pu2clr/Magnetic_Loop_Antenna_Tuner/images/bluetooth_hc05.jpg

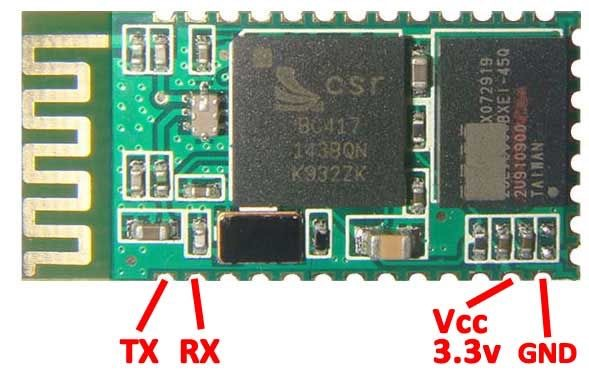
images/bluetooth_hc05.jpg
