pu2clr/Magnetic_Loop_Antenna_Tuner/images/BTAndroid00.png

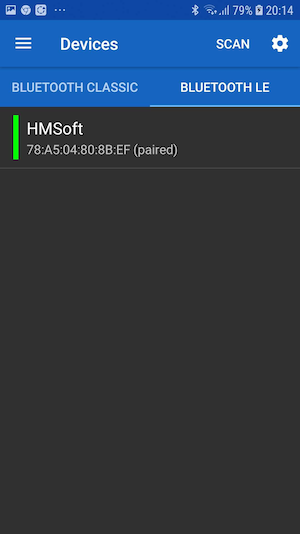
images/BTAndroid00.png
