pu2clr/Magnetic_Loop_Antenna_Tuner/images/photo01.jpg

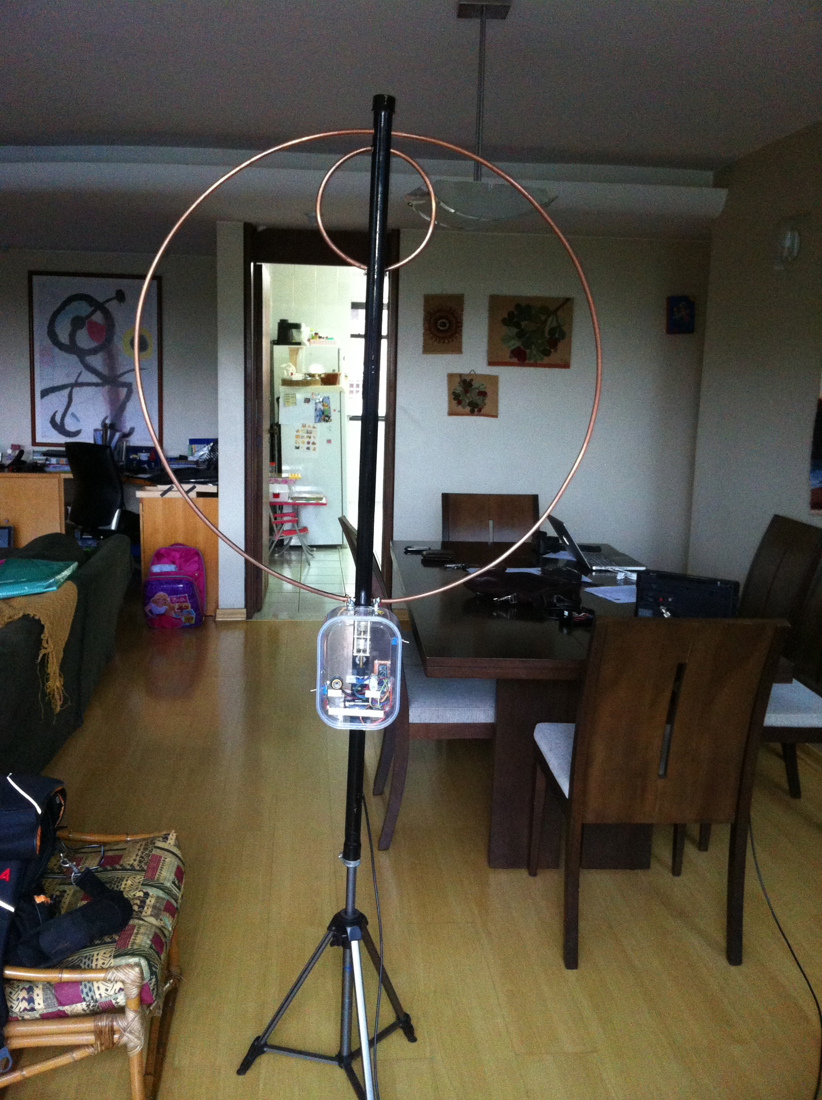
images/photo01.jpg
