pu2clr/Magnetic_Loop_Antenna_Tuner/images/photo02.jpg

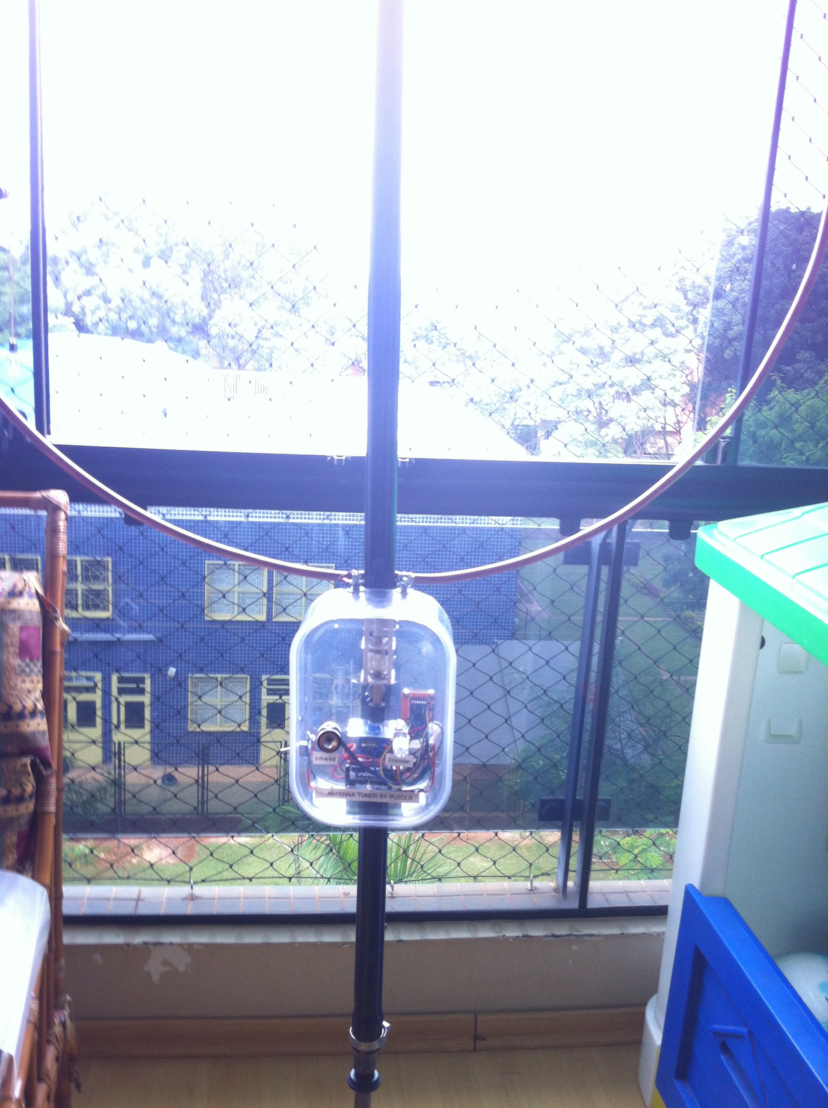
images/photo02.jpg
