pu2clr/Magnetic_Loop_Antenna_Tuner/images/photo03.jpg

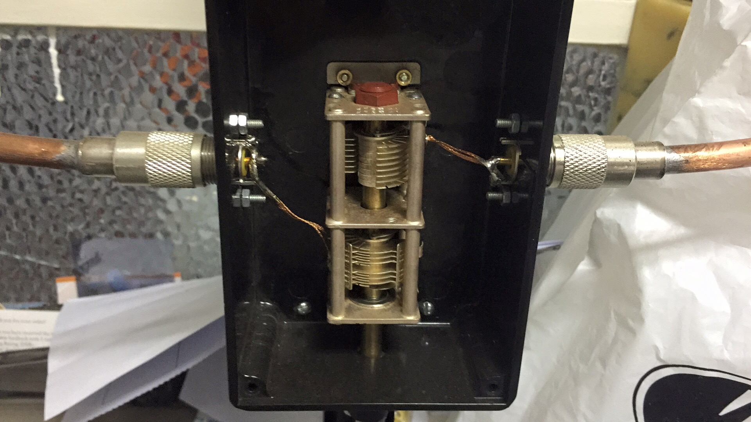
images/photo03.jpg
