pu2clr/Magnetic_Loop_Antenna_Tuner/images/photo04.jpg

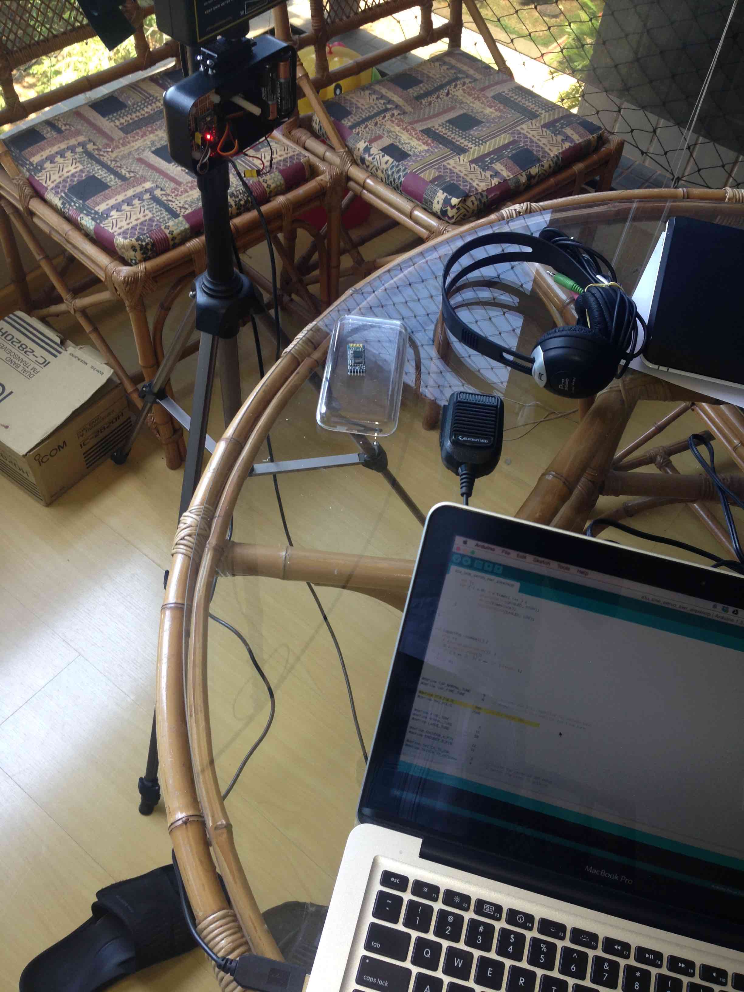
images/photo04.jpg
