pu2clr/Magnetic_Loop_Antenna_Tuner/images/photo06.jpg

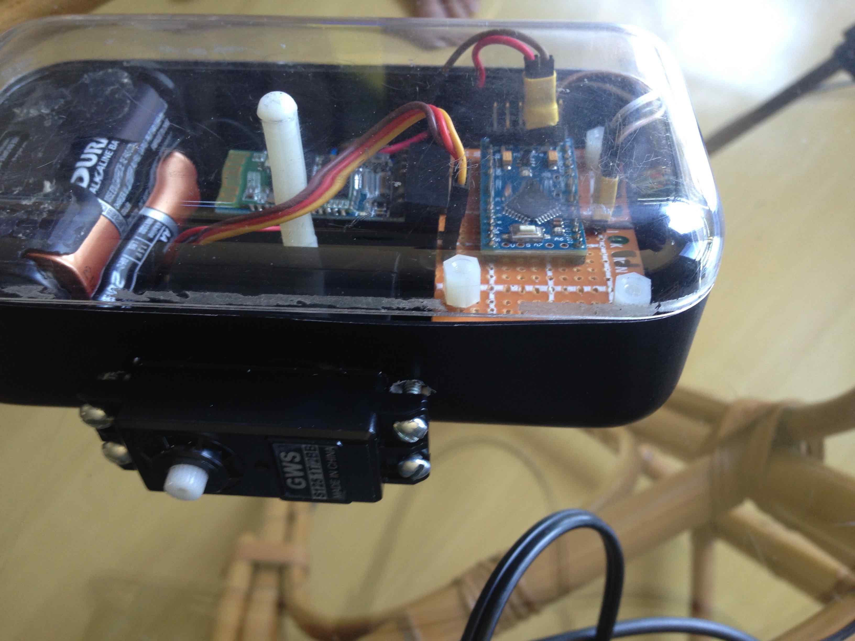
images/photo06.jpg
