pu2clr/Magnetic_Loop_Antenna_Tuner/images/photo07.jpg

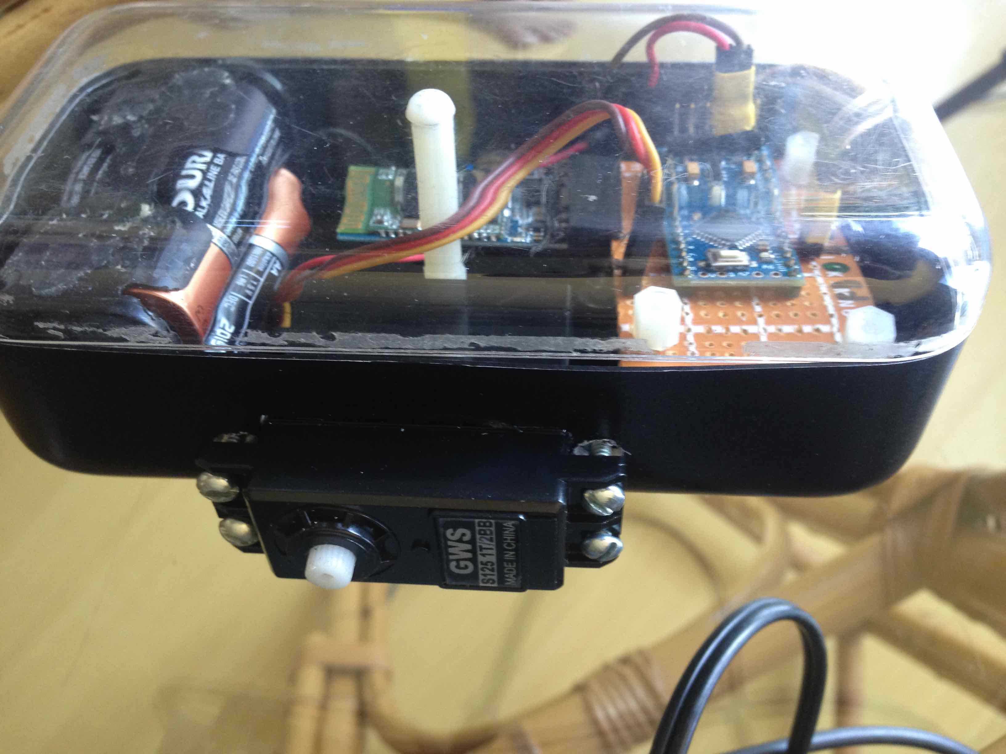
images/photo07.jpg
