pu2clr/Magnetic_Loop_Antenna_Tuner/images/photo08.jpg

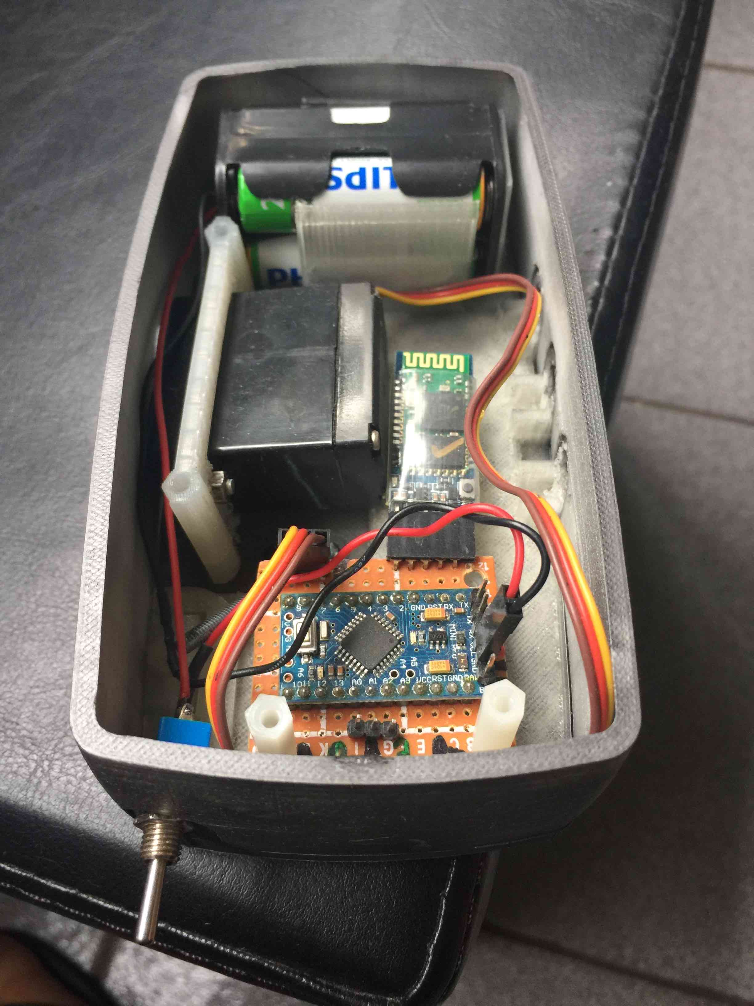
images/photo08.jpg
