pu2clr/Magnetic_Loop_Antenna_Tuner/images/photo11.jpg

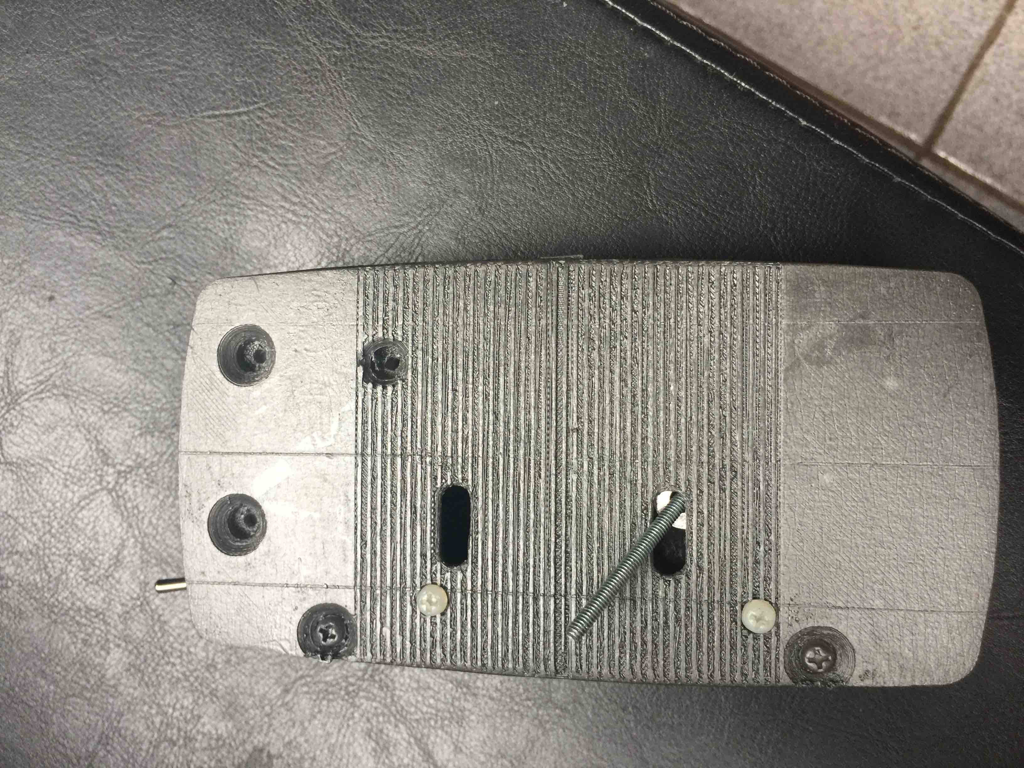
images/photo11.jpg
