pu2clr/Magnetic_Loop_Antenna_Tuner/images/towCap02.jpg

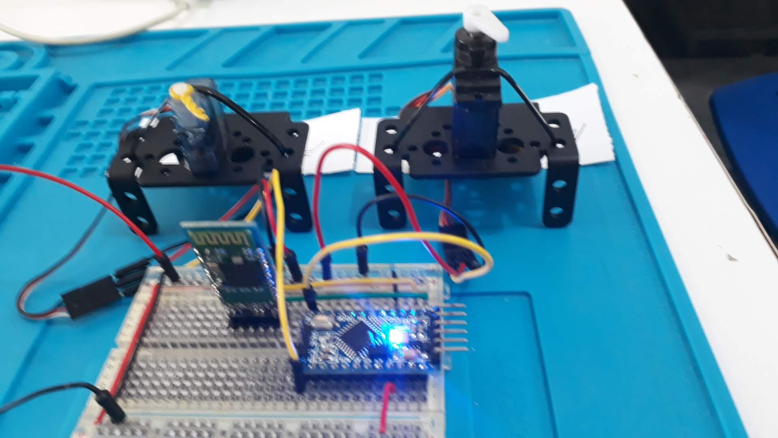
images/towCap02.jpg
