pu2clr/Magnetic_Loop_Antenna_Tuner/images/twoCap01.jpg

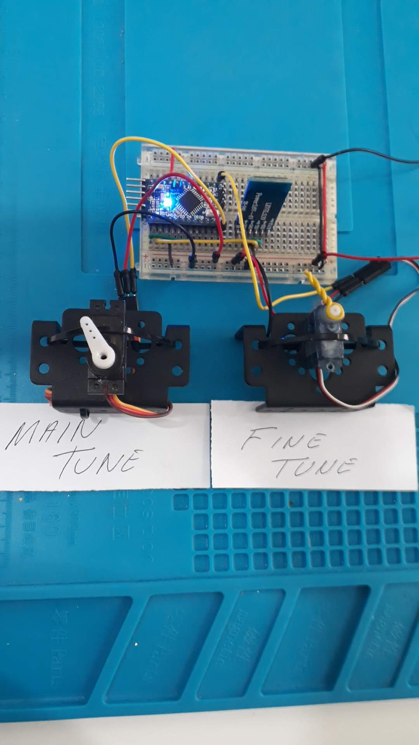
images/twoCap01.jpg
