pu2clr/Magnetic_Loop_Antenna_Tuner/Box_3D_Printer/3D/Final_Version/base.STL

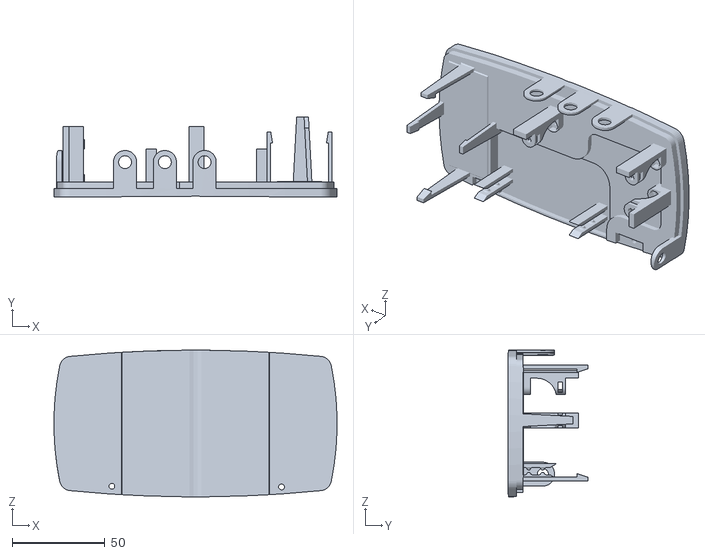
[picture p48: CAD file, 2019-04-02]
Box_3D_Printer/3D/Final_Version/base.STL
152.3 x 43.1 x 78.9
