pu2clr/Magnetic_Loop_Antenna_Tuner/Box_3D_Printer/3D/Final_Version/coupler.STL

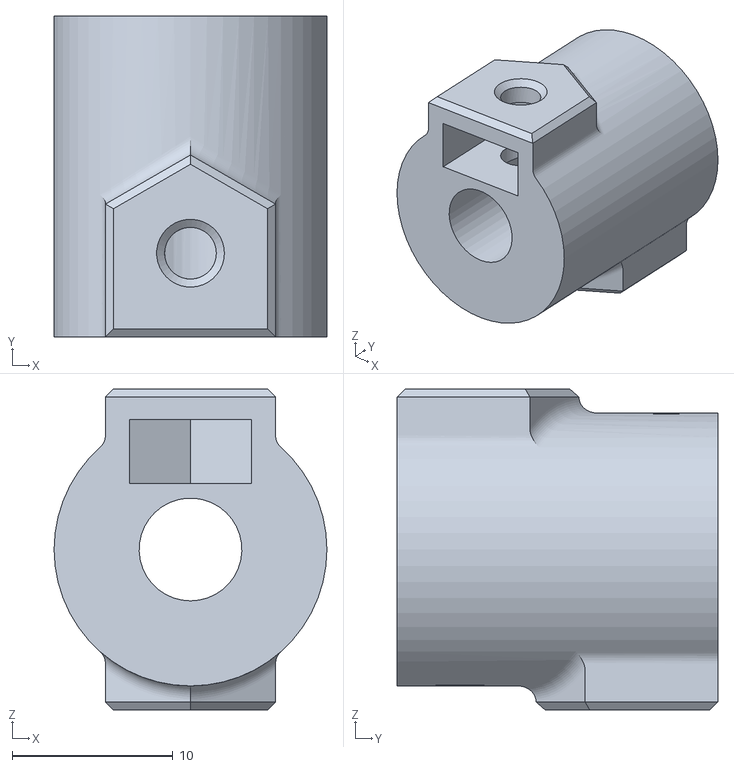
[picture p49: CAD file, 2019-04-02]
Box_3D_Printer/3D/Final_Version/coupler.STL
17.0 x 20.0 x 20.0
