pu2clr/Magnetic_Loop_Antenna_Tuner/Box_3D_Printer/3D/Final_Version/case-lateral.STL

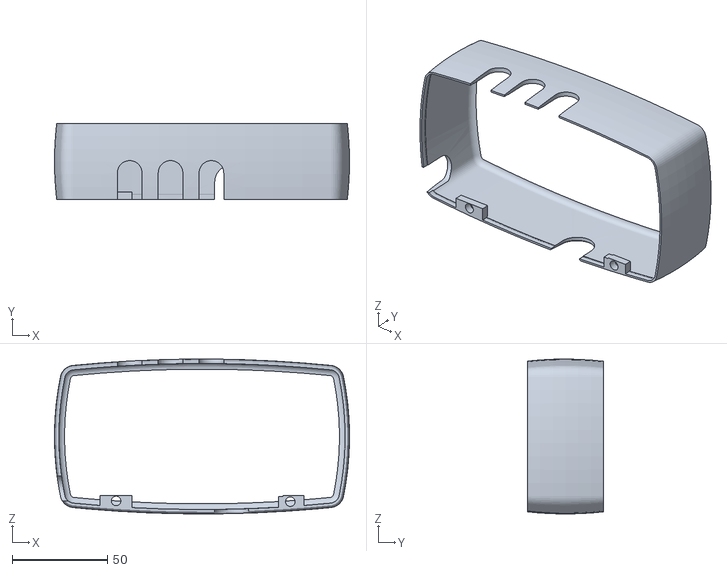
[picture p50: CAD file, 2019-04-02]
Box_3D_Printer/3D/Final_Version/case-lateral.STL
154.6 x 40.0 x 81.2
