pu2clr/Magnetic_Loop_Antenna_Tuner/Box_3D_Printer/3D/Final_Version/base-07maio.STL

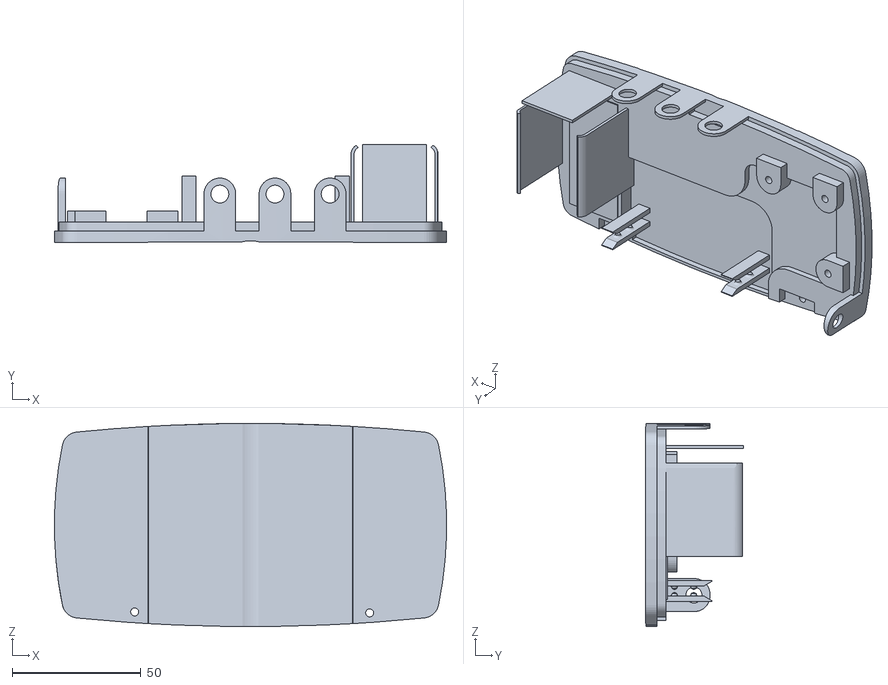
[picture p51: CAD file, 2019-04-02]
Box_3D_Printer/3D/Final_Version/base-07maio.STL
152.3 x 38.0 x 78.9
