pu2clr/Magnetic_Loop_Antenna_Tuner/Box_3D_Printer/3D/Final_Version/suporte.STL

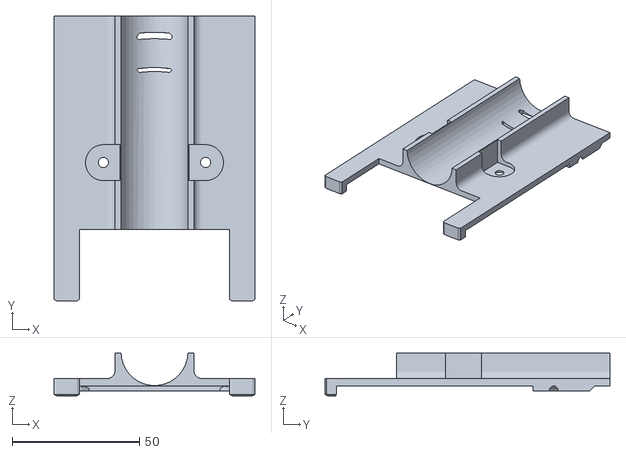
[picture p52: CAD file, 2019-04-02]
Box_3D_Printer/3D/Final_Version/suporte.STL
79.0 x 112.0 x 16.9
