pu2clr/Magnetic_Loop_Antenna_Tuner/Box_3D_Printer/Draft/1.png

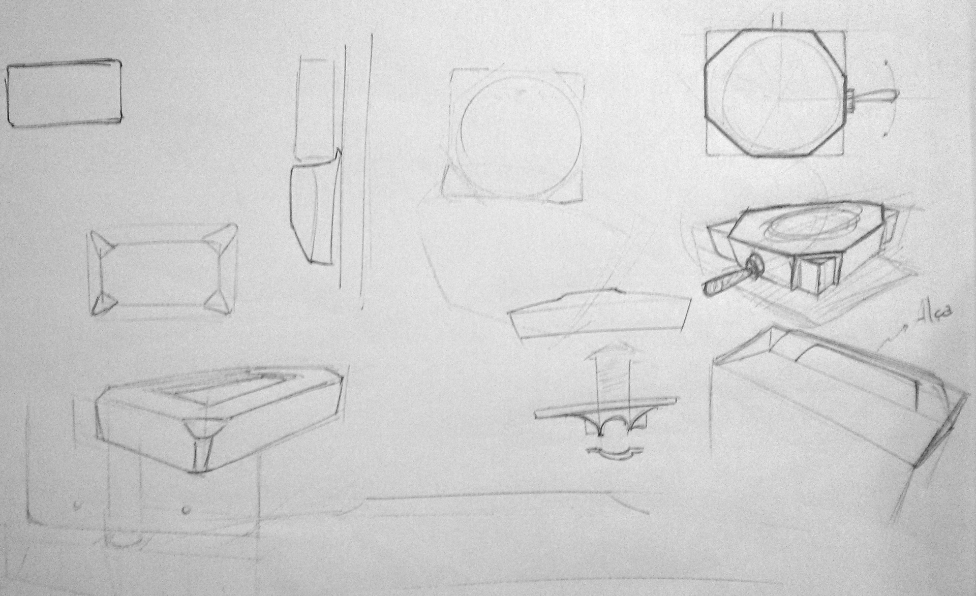
Box_3D_Printer/Draft/1.png
