pu2clr/Magnetic_Loop_Antenna_Tuner/Box_3D_Printer/Renderings/untitled.217.jpg

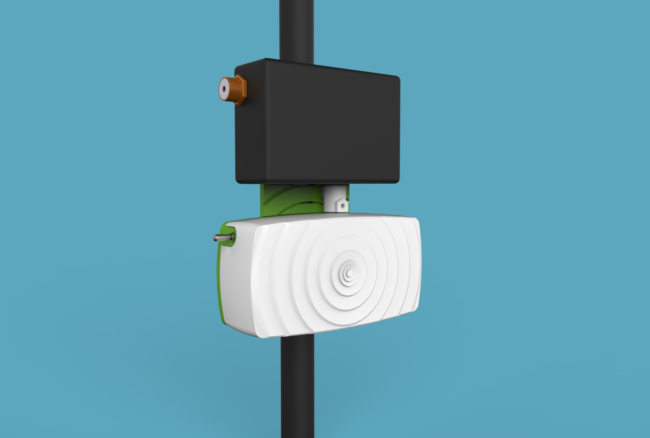
Box_3D_Printer/Renderings/untitled.217.jpg
